salonis13/CUBIT_low_power/images/20220211_230616.jpg

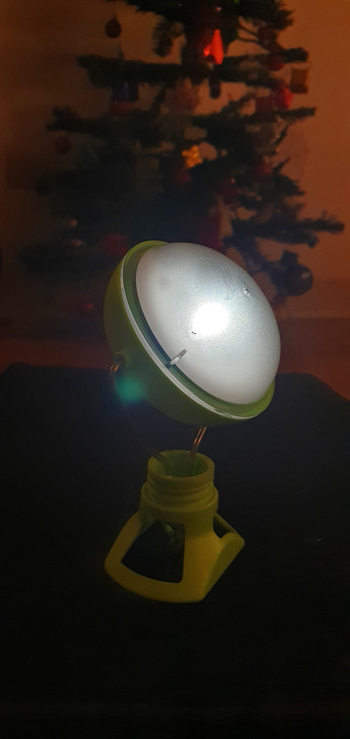
images/20220211_230616.jpg
