salonis13/CUBIT_low_power/images/20220211_230722.jpg

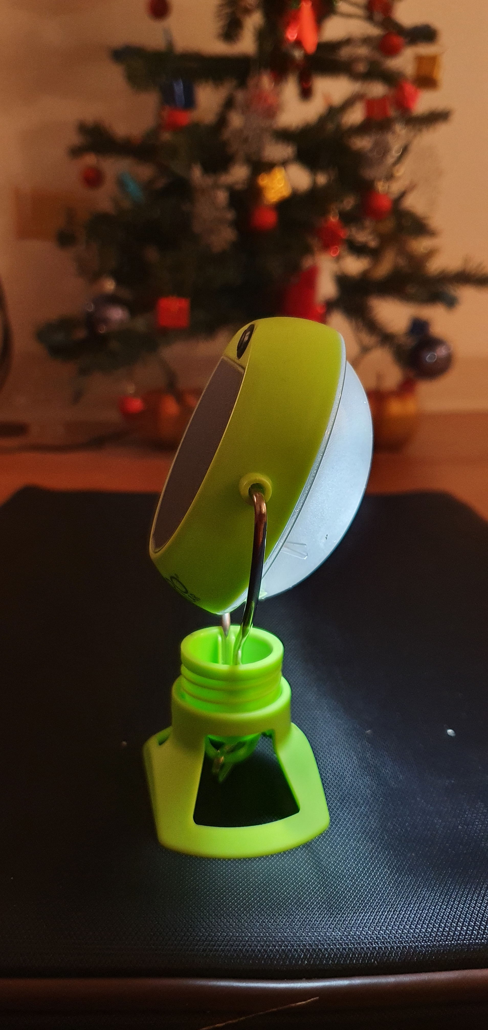
images/20220211_230722.jpg
