salonis13/CUBIT_low_power/images/20220211_230730.jpg

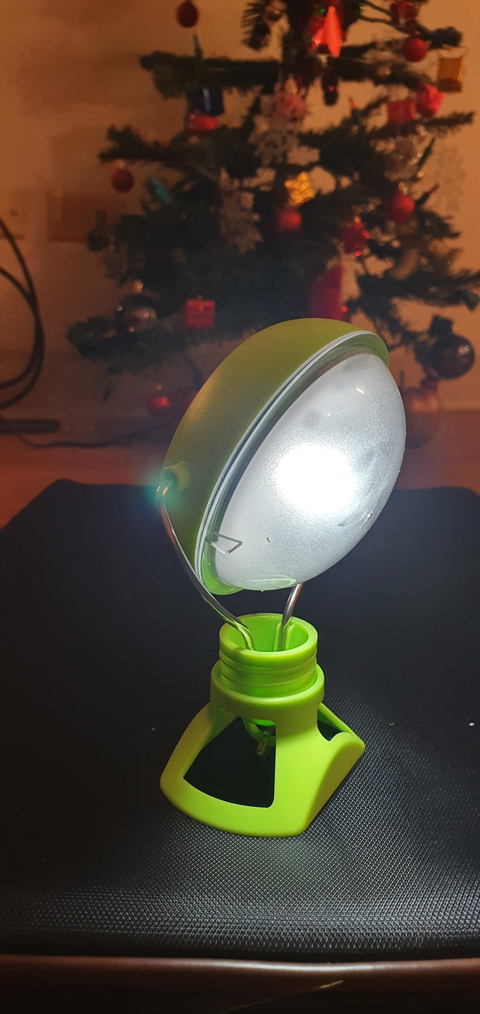
images/20220211_230730.jpg
