salonis13/CUBIT_low_power/images/20220218_140802.jpg

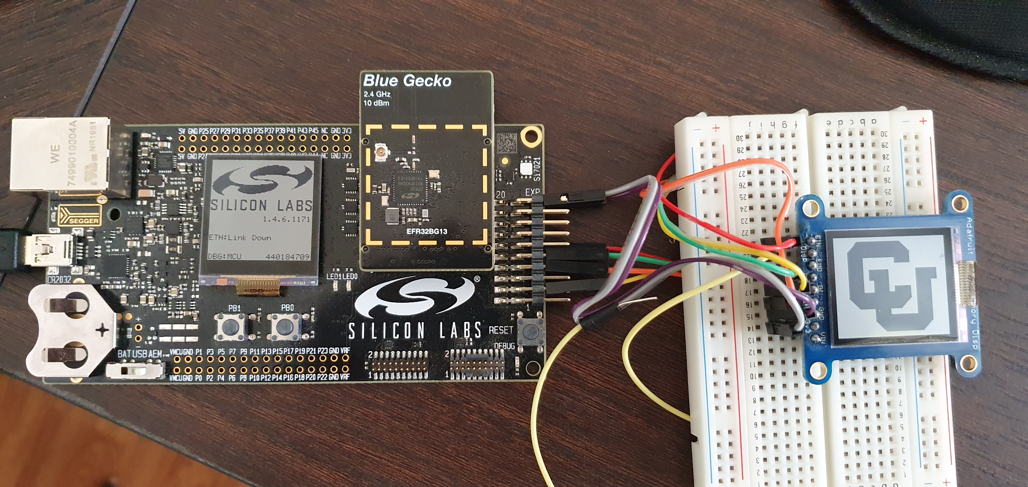
images/20220218_140802.jpg
