salonis13/CUBIT_low_power/images/20220218_140817.jpg

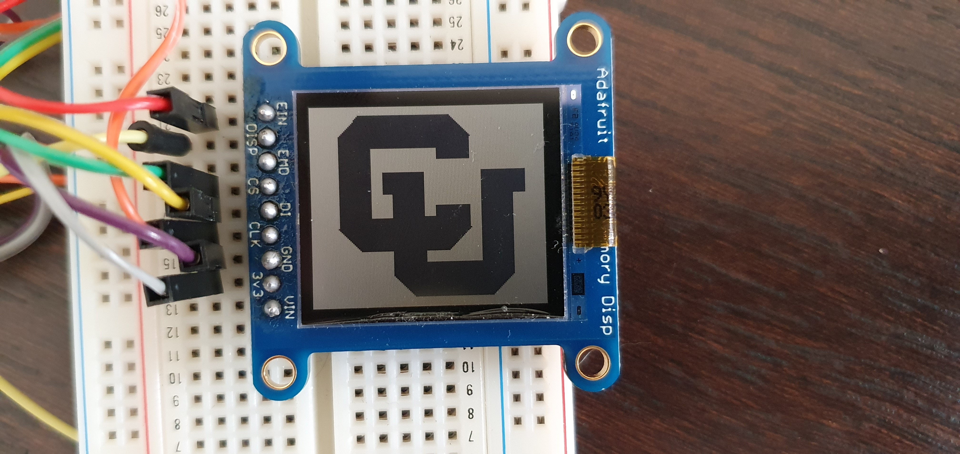
images/20220218_140817.jpg
