salonis13/CUBIT_low_power/images/20220219_193055.jpg

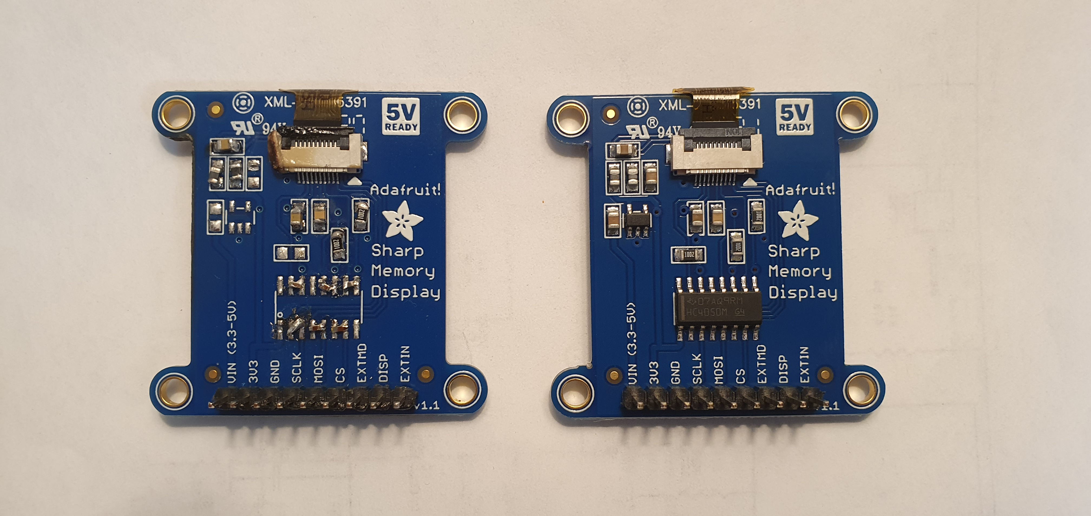
images/20220219_193055.jpg
