salonis13/CUBIT_low_power/images/20220226_095042.jpg

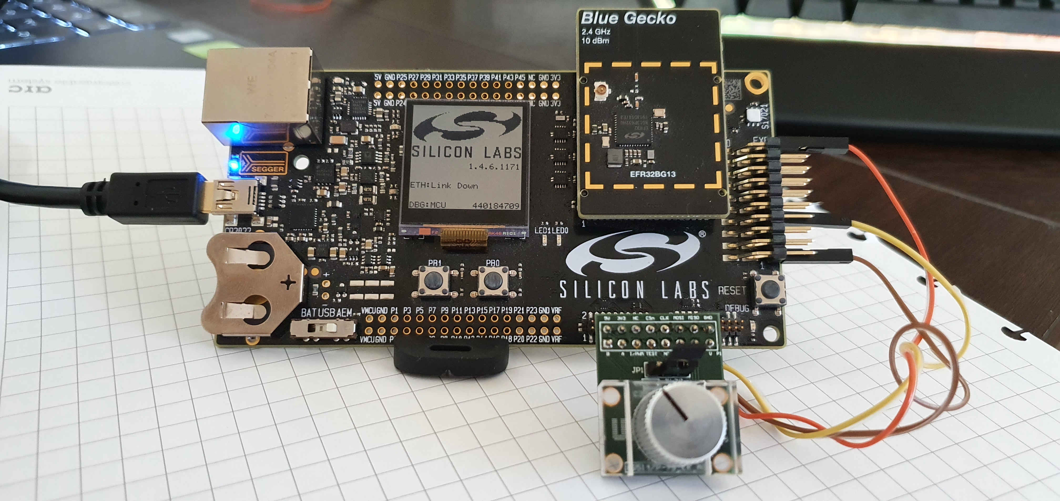
images/20220226_095042.jpg
