salonis13/CUBIT_low_power/images/20220226_095246.jpg

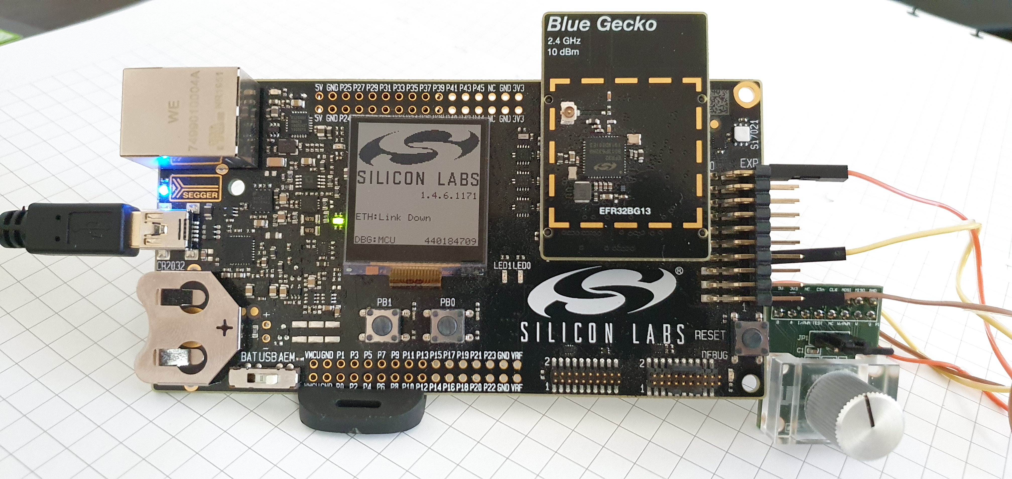
images/20220226_095246.jpg
