salonis13/CUBIT_low_power/images/20220226_104828.jpg

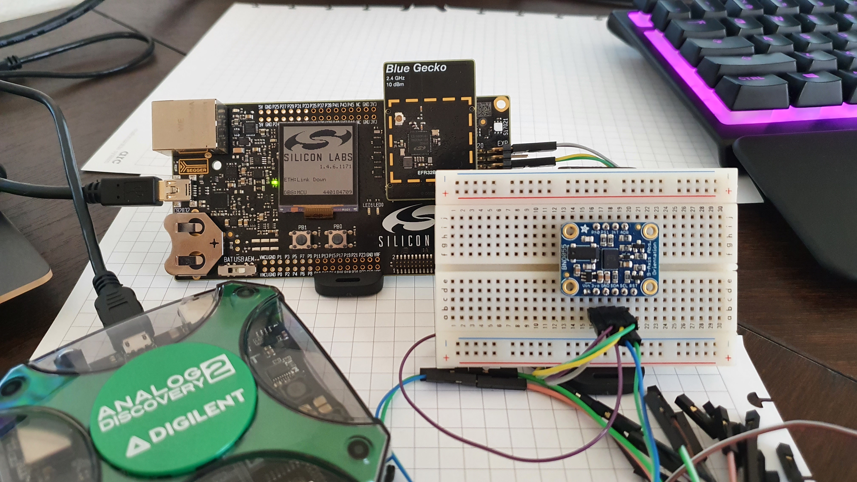
images/20220226_104828.jpg
