salonis13/CUBIT_low_power/images/imu_i2c.png

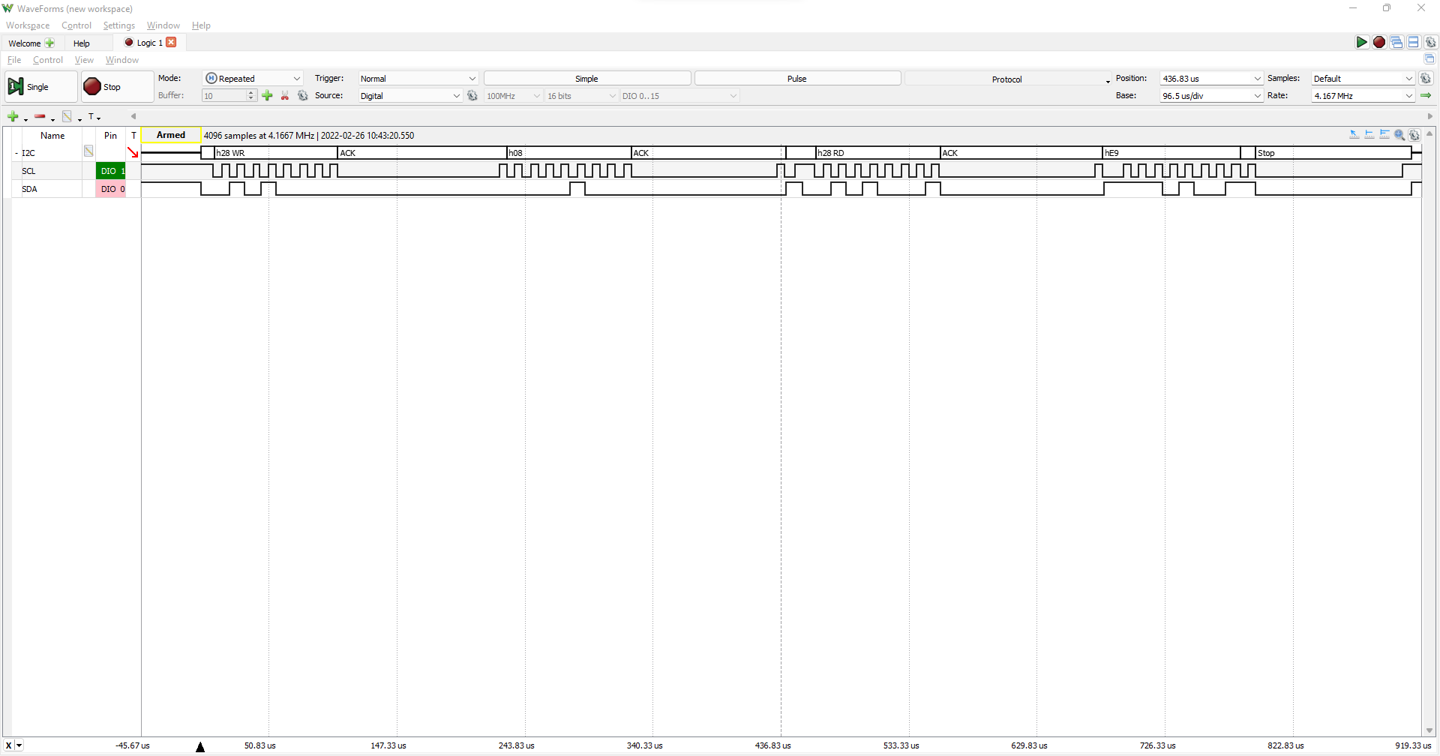
images/imu_i2c.png
