salonis13/CUBIT_low_power/images/mag enc arduino pwm 1.png

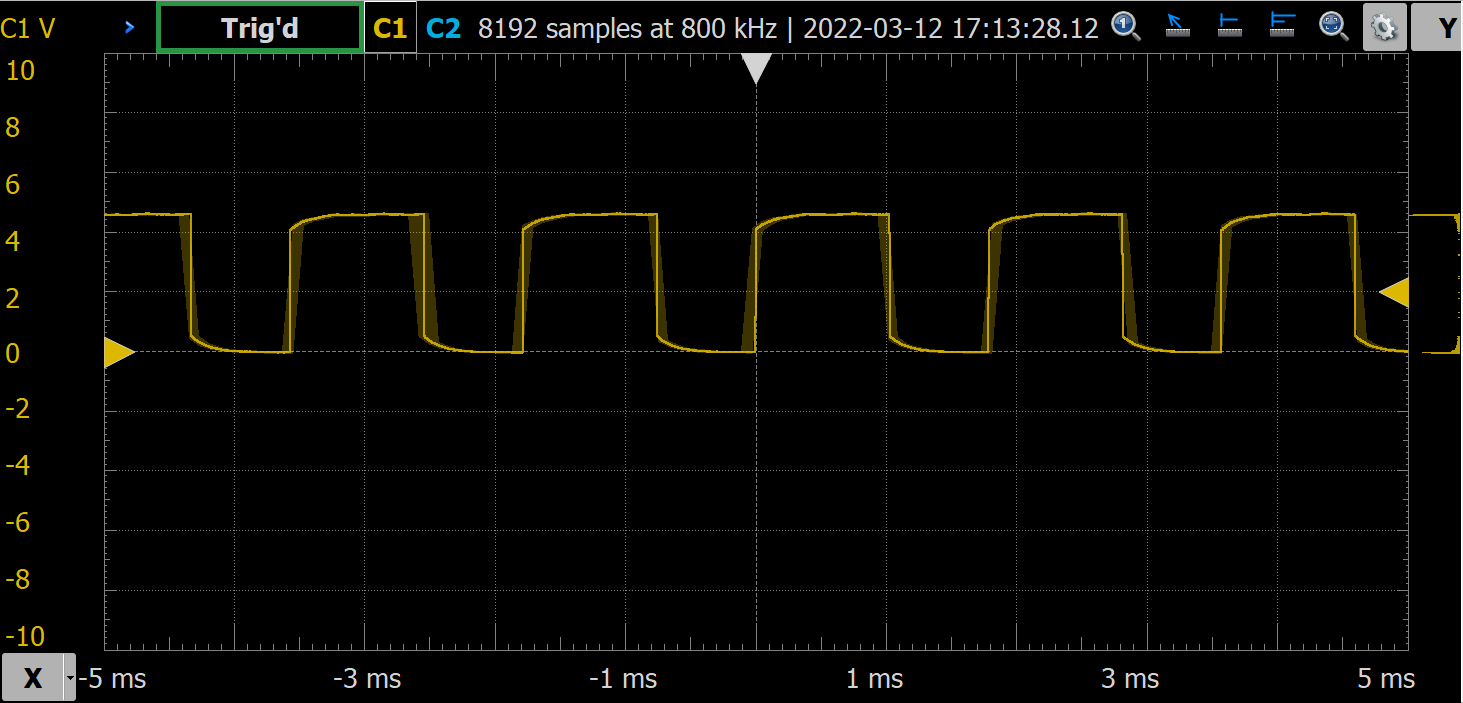
images/mag enc arduino pwm 1.png
