salonis13/CUBIT_low_power/images/mag enc arduino pwm 3.png

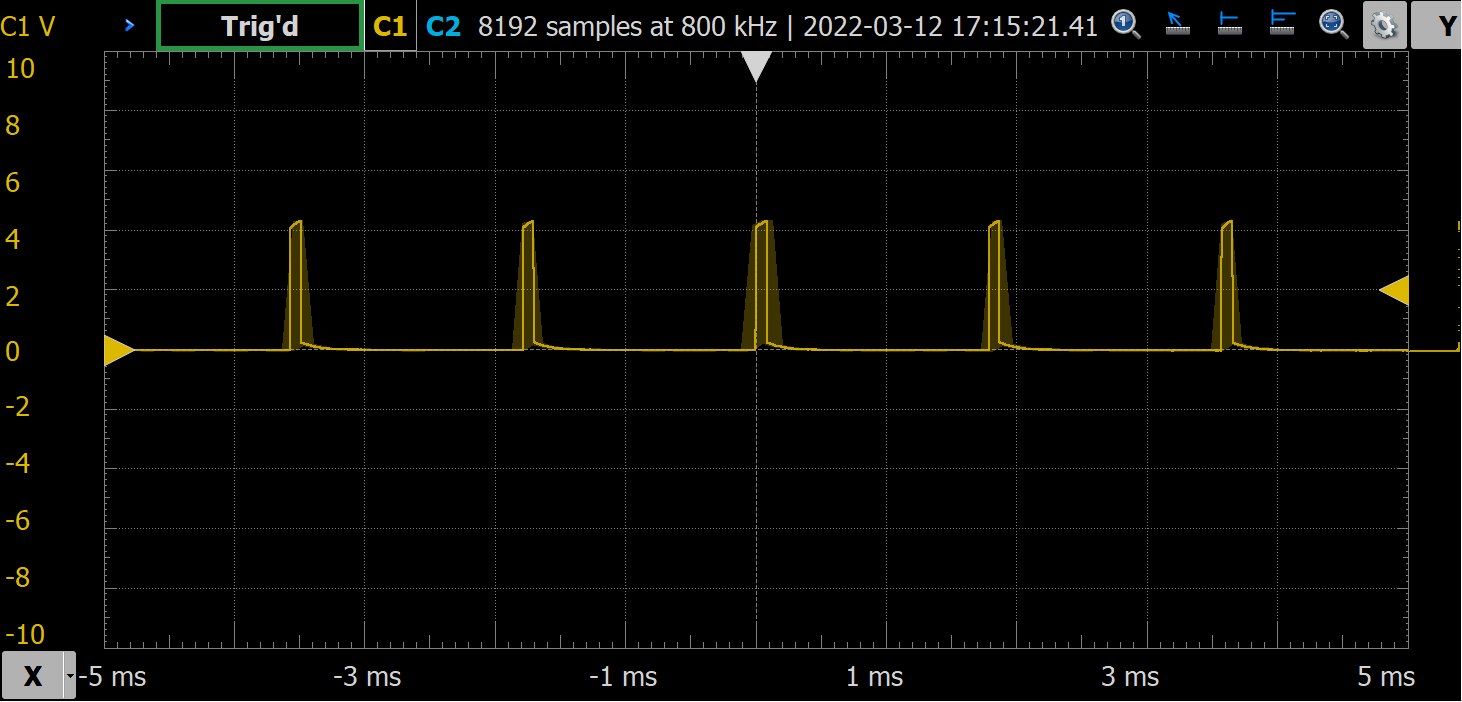
images/mag enc arduino pwm 3.png
