salonis13/CUBIT_low_power/images/Magnetic Encoder energy profile.png

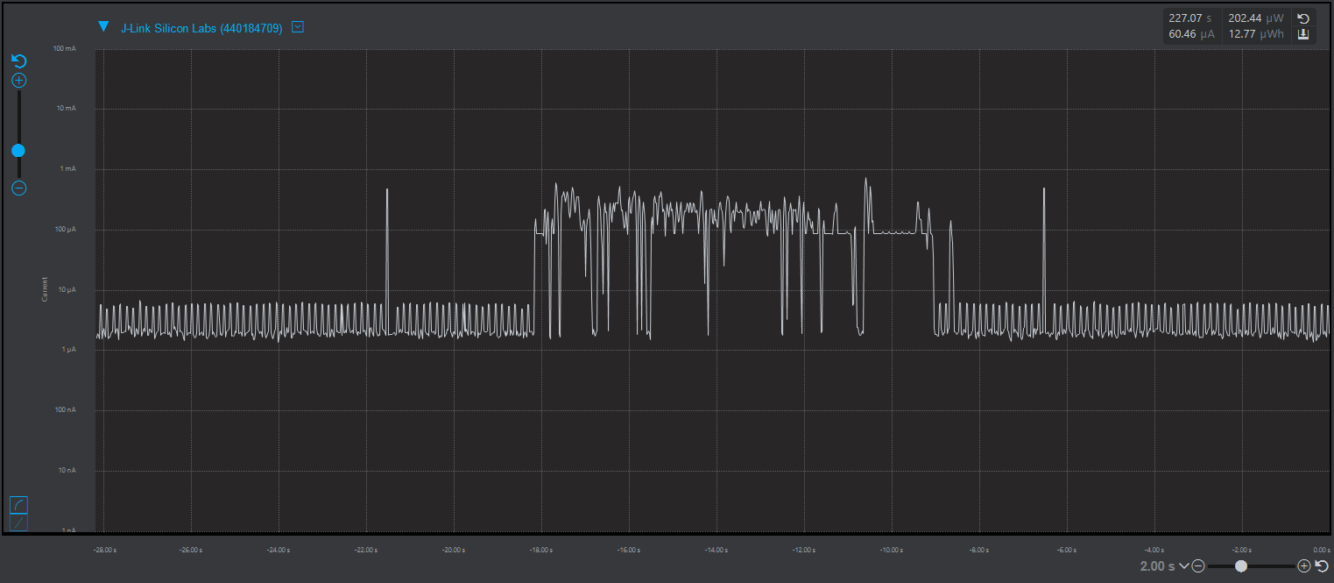
images/Magnetic Encoder energy profile.png
