salonis13/CUBIT_low_power/images/Magnetic Encoder pulses on serial_mod.jpg

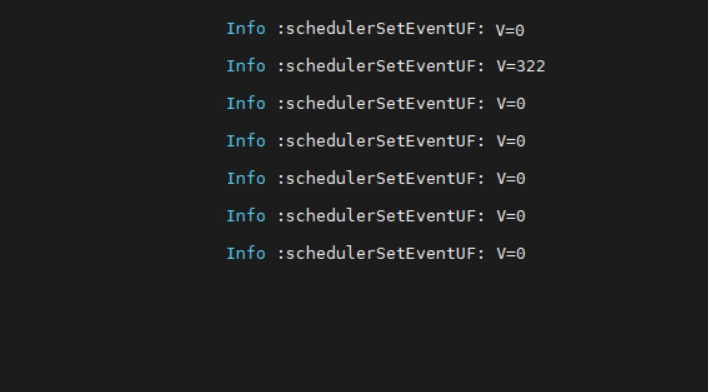
images/Magnetic Encoder pulses on serial_mod.jpg
