salonis13/CUBIT_low_power/images/Screenshot_20220219-193332_WhatsApp.jpg

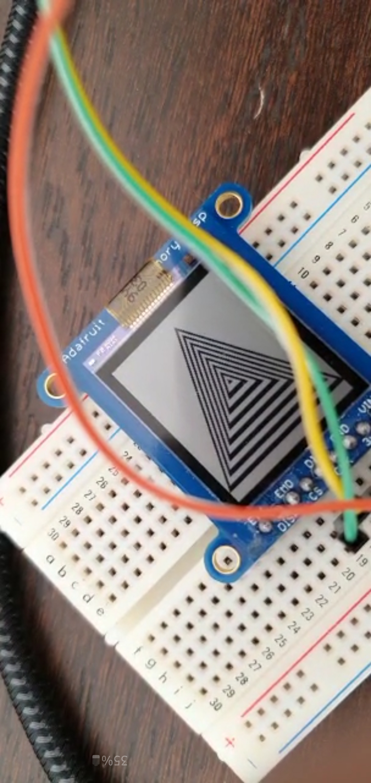
images/Screenshot_20220219-193332_WhatsApp.jpg
