salonis13/CUBIT_low_power/utilities/LCD/CU.png

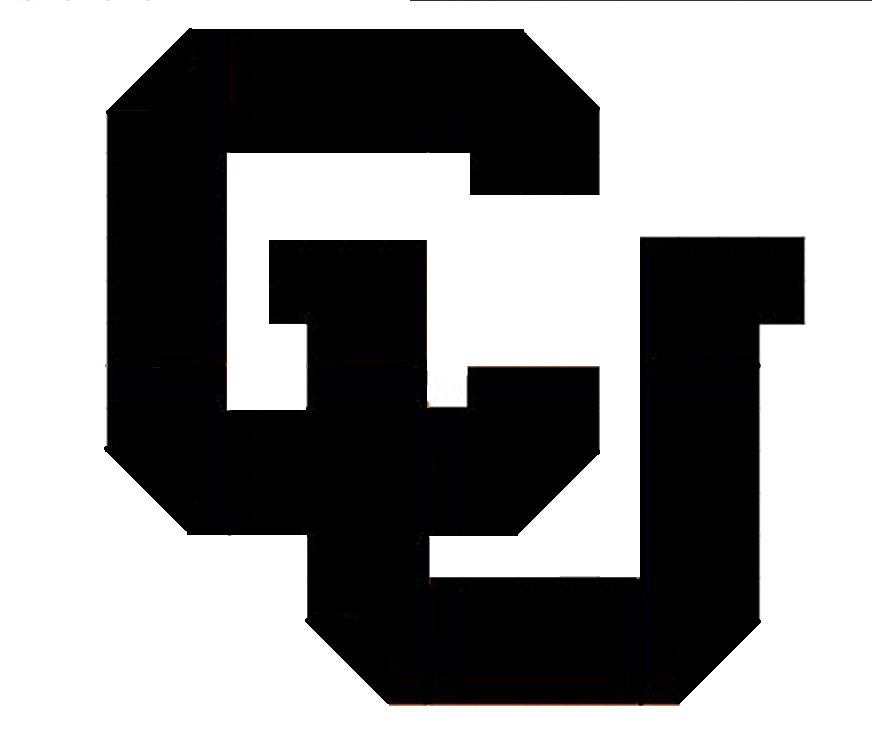
utilities/LCD/CU.png
