salonis13/CUBIT_low_power/utilities/LCD/ff.png

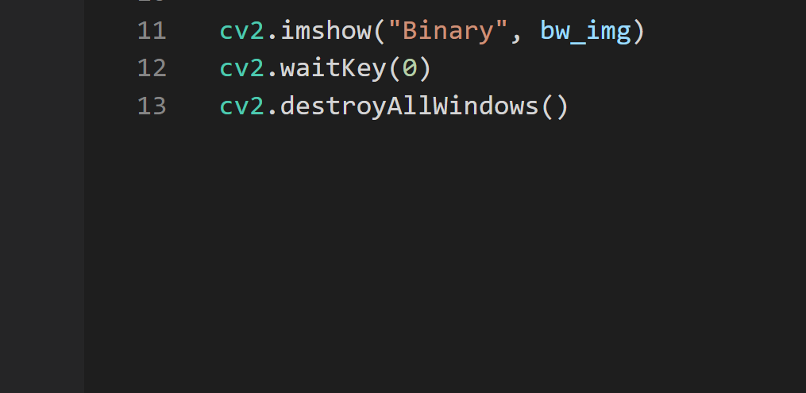
utilities/LCD/ff.png
