salonis13/CUBIT_low_power/software/LTSpice_simulation/Power regV2.asc

C2: cap; 50µ
C3: cap; 47n
C4: cap; 1µ
C5: cap; 150µF
I2: current; PULSE(0 25ma 10ms 1u 1u 10s 13s 4)
L1: ind; 120µ; Rser=1
R3: res; 301k
R4: res; 110k
R5: res; 100k
R6: res; 0.92Meg
R7: res; 2
R8: res; 1.6
Rload1: res; 300e3
U1: LT8604
V1: battery; 3.7; Rser=35
Named nets: 0, OUT, PG, FB, SW, RT, TRSS
.tran 0 13s 0
