salonis13/CUBIT_low_power/software/software_ultrasonic/src/i2c.h

/*
 * i2c.h
 *
 *  Created on: Sep 16, 2021
 *      Author: salon
 */

#ifndef SRC_I2C_H_
#define SRC_I2C_H_

#include "src/timers.h"
#include "src/oscillators.h"
#include "src/gpio.h"
#include "app.h"

#include "em_letimer.h"
#include "em_gpio.h"
#include "sl_i2cspm.h"
#include "em_i2c.h"
#include "main.h"

//function to initialize I2C peripheral
void i2c_init();

//function to convert data in temperature value
float convertTemp();

//function to write a command to slave
void write_cmd();

void i2c_write(uint8_t address, uint8_t cmd);

I2C_TransferReturn_TypeDef i2c_write_write(uint8_t address, uint8_t reg, uint8_t value);
I2C_TransferReturn_TypeDef i2c_read(uint8_t address, uint8_t* data_buffer);
I2C_TransferReturn_TypeDef i2c_write_read(uint8_t address, uint8_t reg, uint8_t* data_read_from_imu);


//function to read temperature from sensor
void read_cmd();

#endif /* SRC_I2C_H_ */
