salonis13/CUBIT_low_power/software/software_ultrasonic/src/scheduler.h

/*
 * scheduler.h
 *
 *  Created on: Sep 15, 2021
 *      Author: salon
 */

#ifndef SRC_SCHEDULER_H_
#define SRC_SCHEDULER_H_

#include "src/timers.h"
#include "src/oscillators.h"
#include "src/gpio.h"
#include "src/ble.h"
#include "app.h"

#include "em_letimer.h"
#include "main.h"

//function to set a scheduler event
void schedulerSetEventUF();

void schedulerSetEventUART();

void schedulerSetEventCOMP1();

void schedulerSetEventTransferDone();

void schedulerSetEventButtonPressed();

void schedulerSetEventButtonReleased();

//function to get scheduler event
uint32_t getNextEvent();

//state machine function
void temperature_state_machine(sl_bt_msg_t *evt);

void discovery_state_machine(sl_bt_msg_t *evt);


#endif /* SRC_SCHEDULER_H_ */
