salonis13/CUBIT_low_power/software/software_ultrasonic/src/ultrasonic.h

/*
 * ultrasonic.h
 *
 *  Created on: Mar 3, 2022
 *      Author: Saloni
 */

#ifndef SRC_ULTRASONIC_H_
#define SRC_ULTRASONIC_H_

//#include "em_leuart.h"


void initGpio(void);

void initUsart2(void);
int get_received_char_usart2(void);
int get_processed_data_from_ultrasonic_sensor(void);



#endif /* SRC_ULTRASONIC_H_ */
