salonis13/CUBIT_low_power/software/source/autogen/sl_component_catalog.h

#ifndef SL_COMPONENT_CATALOG_H
#define SL_COMPONENT_CATALOG_H

// APIs present in project
#define SL_CATALOG_APP_ASSERT_PRESENT
#define SL_CATALOG_APP_LOG_PRESENT
#define SL_CATALOG_BLUETOOTH_FEATURE_ADVERTISER_PRESENT
#define SL_CATALOG_BLUETOOTH_FEATURE_CONNECTION_PRESENT
#define SL_CATALOG_BLUETOOTH_PRESENT
#define SL_CATALOG_DEVICE_INIT_NVIC_PRESENT
#define SL_CATALOG_EMLIB_CORE_DEBUG_CONFIG_PRESENT
#define SL_CATALOG_GATT_CONFIGURATION_PRESENT
#define SL_CATALOG_GLIB_PRESENT
#define SL_CATALOG_IOSTREAM_UART_COMMON_PRESENT
#define SL_CATALOG_IOSTREAM_USART_PRESENT
#define SL_CATALOG_MEMLCD_USART_PRESENT
#define SL_CATALOG_MPU_PRESENT
#define SL_CATALOG_POWER_MANAGER_PRESENT
#define SL_CATALOG_LED0_PRESENT
#define SL_CATALOG_SIMPLE_LED_PRESENT
#define SL_CATALOG_SLEEPTIMER_PRESENT

#endif // SL_COMPONENT_CATALOG_H
